DanielMartensson/STM32-Ethernet-Camera/Code/Core/Src/STM32_ILI9341_FSMC_16_Bit/ili9341.c

	/*
 * ili9341.c
 *
 *  Created on: 22 ���. 2018 �.
 *      Author: Andriy Honcharenko
 */
#include "../STM32_ILI9341_FSMC_16_Bit/ili9341.h"

#include <stdlib.h>
#include <stdarg.h>
#include <stdio.h>

/* Axis measurement */
#define CMD_X_AXIS								0x50
#define CMD_Y_AXIS								0x10
#define CMD_Z_AXIS								0x30

/* For the touch */
SPI_HandleTypeDef *_hspi;

enum {
  MemoryAccessControlNormalOrder,
  MemoryAccessControlReverseOrder
} MemoryAccessControlRefreshOrder;

enum {
	MemoryAccessControlColorOrderRGB,
	MemoryAccessControlColorOrderBGR
} MemoryAccessControlColorOrder;

static lcdPropertiesTypeDef  lcdProperties = { ILI9341_PIXEL_WIDTH, ILI9341_PIXEL_HEIGHT, LCD_ORIENTATION_PORTRAIT,true, true };
static lcdFontPropTypeDef lcdFont = {COLOR_YELLOW, COLOR_BLACK, &Font12, 1};
static lcdCursorPosTypeDef cursorXY = {0, 0};

static unsigned char lcdPortraitConfig = 0;
static unsigned char lcdLandscapeConfig = 0;
static unsigned char lcdPortraitMirrorConfig = 0;
static unsigned char lcdLandscapeMirrorConfig = 0;

static void				lcdDrawPixels(uint16_t x, uint16_t y, uint16_t *data, uint32_t dataLength);
static void        		lcdReset(void);
static void        		lcdWriteCommand(unsigned char command);
static void             lcdWriteData(unsigned short data);
static unsigned short	lcdReadData(void);

static unsigned char    lcdBuildMemoryAccessControlConfig(
                                bool rowAddressOrder,
                                bool columnAddressOrder,
                                bool rowColumnExchange,
                                bool verticalRefreshOrder,
                                bool colorOrder,
                                bool horizontalRefreshOrder);


void lcdInit(SPI_HandleTypeDef *hspi)
{
	/* Set touch SPI */
	_hspi = hspi;

  lcdPortraitConfig = lcdBuildMemoryAccessControlConfig(
                                                    MemoryAccessControlNormalOrder,		// rowAddressOrder
                                                    MemoryAccessControlReverseOrder,	// columnAddressOrder
                                                    MemoryAccessControlNormalOrder,		// rowColumnExchange
                                                    MemoryAccessControlNormalOrder,		// verticalRefreshOrder
                                                    MemoryAccessControlColorOrderBGR,	// colorOrder
                                                    MemoryAccessControlNormalOrder);	// horizontalRefreshOrder

  lcdLandscapeConfig = lcdBuildMemoryAccessControlConfig(
                                                    MemoryAccessControlNormalOrder,		// rowAddressOrder
                                                    MemoryAccessControlNormalOrder,		// columnAddressOrder
                                                    MemoryAccessControlReverseOrder,	// rowColumnExchange
                                                    MemoryAccessControlNormalOrder,		// verticalRefreshOrder
                                                    MemoryAccessControlColorOrderBGR,	// colorOrder
                                                    MemoryAccessControlNormalOrder);	// horizontalRefreshOrder

  lcdPortraitMirrorConfig = lcdBuildMemoryAccessControlConfig(
		  	  	  	  	  	  	  	  	  	  	  	MemoryAccessControlReverseOrder,	// rowAddressOrder
		                                            MemoryAccessControlNormalOrder,		// columnAddressOrder
		                                            MemoryAccessControlNormalOrder,		// rowColumnExchange
		                                            MemoryAccessControlNormalOrder,		// verticalRefreshOrder
		                                            MemoryAccessControlColorOrderBGR,	// colorOrder
		                                            MemoryAccessControlNormalOrder);	// horizontalRefreshOrder

  lcdLandscapeMirrorConfig = lcdBuildMemoryAccessControlConfig(
                                                    MemoryAccessControlReverseOrder,	// rowAddressOrder
                                                    MemoryAccessControlReverseOrder,	// columnAddressOrder
                                                    MemoryAccessControlReverseOrder,	// rowColumnExchange
                                                    MemoryAccessControlNormalOrder,		// verticalRefreshOrder
                                                    MemoryAccessControlColorOrderBGR,	// colorOrder
                                                    MemoryAccessControlNormalOrder);	// horizontalRefreshOrder

  lcdReset();

  lcdWriteCommand(ILI9341_DISPLAYOFF);

  lcdWriteCommand(0xCF);
  lcdWriteData(0x00);
  lcdWriteData(0x83);
  lcdWriteData(0x30);

  lcdWriteCommand(0xED);
  lcdWriteData(0x64);
  lcdWriteData(0x03);
  lcdWriteData(0x12);
  lcdWriteData(0x81);

  lcdWriteCommand(0xE8);
  lcdWriteData(0x85);
  lcdWriteData(0x01);
  lcdWriteData(0x79);

  lcdWriteCommand(0xCB);
  lcdWriteData(0x39);
  lcdWriteData(0x2C);
  lcdWriteData(0x00);
  lcdWriteData(0x34);
  lcdWriteData(0x02);

  lcdWriteCommand(0xF7);
  lcdWriteData(0x20);

  lcdWriteCommand(0xEA);
  lcdWriteData(0x00);
  lcdWriteData(0x00);

  lcdWriteCommand(ILI9341_POWERCONTROL1);
  lcdWriteData(0x26);

  lcdWriteCommand(ILI9341_POWERCONTROL2);
  lcdWriteData(0x11);

  lcdWriteCommand(ILI9341_VCOMCONTROL1);
  lcdWriteData(0x35);
  lcdWriteData(0x3E);

  lcdWriteCommand(ILI9341_VCOMCONTROL2);
  lcdWriteData(0xBE);

  lcdWriteCommand(ILI9341_MEMCONTROL);
  lcdWriteData(lcdPortraitConfig);

  lcdWriteCommand(ILI9341_PIXELFORMAT);
  lcdWriteData(0x55);

  lcdWriteCommand(ILI9341_FRAMECONTROLNORMAL);
  lcdWriteData(0x00);
  lcdWriteData(0x1B);

  lcdWriteCommand(0xF2);
  lcdWriteData(0x08);

  lcdWriteCommand(ILI9341_GAMMASET);
  lcdWriteData(0x01);

  lcdWriteCommand(ILI9341_POSITIVEGAMMCORR);
  lcdWriteData(0x1F);
  lcdWriteData(0x1A);
  lcdWriteData(0x18);
  lcdWriteData(0x0A);
  lcdWriteData(0x0F);
  lcdWriteData(0x06);
  lcdWriteData(0x45);
  lcdWriteData(0x87);
  lcdWriteData(0x32);
  lcdWriteData(0x0A);
  lcdWriteData(0x07);
  lcdWriteData(0x02);
  lcdWriteData(0x07);
  lcdWriteData(0x05);
  lcdWriteData(0x00);

  lcdWriteCommand(ILI9341_NEGATIVEGAMMCORR);
  lcdWriteData(0x00);
  lcdWriteData(0x25);
  lcdWriteData(0x27);
  lcdWriteData(0x05);
  lcdWriteData(0x10);
  lcdWriteData(0x09);
  lcdWriteData(0x3A);
  lcdWriteData(0x78);
  lcdWriteData(0x4D);
  lcdWriteData(0x05);
  lcdWriteData(0x18);
  lcdWriteData(0x0D);
  lcdWriteData(0x38);
  lcdWriteData(0x3A);
  lcdWriteData(0x1F);

  lcdWriteCommand(ILI9341_COLADDRSET);
  lcdWriteData(0x00);
  lcdWriteData(0x00);
  lcdWriteData(0x00);
  lcdWriteData(0xEF);

  lcdWriteCommand(ILI9341_PAGEADDRSET);
  lcdWriteData(0x00);
  lcdWriteData(0x00);
  lcdWriteData(0x01);
  lcdWriteData(0x3F);

  lcdWriteCommand(ILI9341_ENTRYMODE);
  lcdWriteData(0x07);

  lcdWriteCommand(ILI9341_DISPLAYFUNC);
  lcdWriteData(0x0A);
  lcdWriteData(0x82);
  lcdWriteData(0x27);
  lcdWriteData(0x00);

  lcdWriteCommand(ILI9341_SLEEPOUT);
  HAL_Delay(100);
  lcdWriteCommand(ILI9341_DISPLAYON);
  HAL_Delay(100);
  lcdWriteCommand(ILI9341_MEMORYWRITE);
}

void lcdTest(void)
{
	lcdSetWindow(0, 0, lcdProperties.width - 1, lcdProperties.height - 1);

	uint8_t stripSize = lcdProperties.height / 8;

	for (int y = 0; y < lcdProperties.height; y++)
	{
		for (int x = 0; x < lcdProperties.width; x++)
		{
		  if (y > lcdProperties.height - 1 - (stripSize * 1)) lcdWriteData(COLOR_WHITE);
		  else if (y > lcdProperties.height - 1 - (stripSize * 2)) lcdWriteData(COLOR_BLUE);
		  else if (y > lcdProperties.height - 1 - (stripSize * 3)) lcdWriteData(COLOR_GREEN);
		  else if (y > lcdProperties.height - 1 - (stripSize * 4)) lcdWriteData(COLOR_CYAN);
		  else if (y > lcdProperties.height - 1 - (stripSize * 5)) lcdWriteData(COLOR_RED);
		  else if (y > lcdProperties.height - 1 - (stripSize * 6)) lcdWriteData(COLOR_MAGENTA);
		  else if (y > lcdProperties.height - 1 - (stripSize * 7)) lcdWriteData(COLOR_YELLOW);
		  else lcdWriteData(COLOR_BLACK);
		}
	}
}

void lcdFillRGB(uint16_t color)
{
  lcdSetWindow(0, 0, lcdProperties.width - 1, lcdProperties.height - 1);
  int dimensions = lcdProperties.width * lcdProperties.height;
  while(dimensions--)
  {
    lcdWriteData(color);
  }
}

/**
 * \brief Draws a point at the specified coordinates
 *
 * \param x        x-Coordinate
 * \param y        y-Coordinate
 * \param color    Color
 *
 * \return void
 */
void lcdDrawPixel(uint16_t x, uint16_t y, uint16_t color)
{
    // Clip
    if ((x < 0) || (y < 0) || (x >= lcdProperties.width) || (y >= lcdProperties.height))
        return;

    lcdSetWindow(x, y, x, y);
    lcdWriteData(color);
}

void lcdDrawHLine(uint16_t x0, uint16_t x1, uint16_t y, uint16_t color)
{
  // Allows for slightly better performance than setting individual pixels

	if (x1 < x0)
	{
		// Switch x1 and x0
		swap(x0, x1);
	}

	// Check limits
	if (x1 >= lcdProperties.width)
	{
		x1 = lcdProperties.width - 1;
	}

	if (x0 >= lcdProperties.width)
	{
		x0 = lcdProperties.width - 1;
	}

	lcdSetWindow(x0, y, x1, y);

	for (int line = x0; line <= x1; line++)
	{
		lcdWriteData(color);
	}
}

void lcdDrawVLine(uint16_t x, uint16_t y0, uint16_t y1, uint16_t color)
{
  if (y1 < y0)
  {
	  swap(y0, y1);
  }

  if (x >= lcdProperties.width)
  {
    x = lcdProperties.width - 1;
  }

  if (y0 >= lcdProperties.height)
  {
    y0 = lcdProperties.height - 1;
  }

  if (y1 >= lcdProperties.height)
  {
    y1 = lcdProperties.height - 1;
  }

  lcdSetWindow(x, y0, x, y1);

  for(int line = y0; line <= y1; line++)
  {
	  lcdWriteData(color);
  }
}

/**
 * \brief Draws a line connecting the two points specified by the coordinate pairs
 *
 * \param x0	The x-coordinate of the first point
 * \param y0	The y-coordinate of the first point
 * \param x1	The x-coordinate of the second point
 * \param y1	The y-coordinate of the second point.
 * \param color	Color
 *
 * \return void
 */
void lcdDrawLine(int16_t x1, int16_t y1, int16_t x2, int16_t y2, uint16_t color)
{
	// Bresenham's algorithm - thx wikpedia

	int16_t steep = abs(y2 - y1) > abs(x2 - x1);
	if (steep)
	{
		swap(x1, y1);
		swap(x2, y2);
	}

	if (x1 > x2)
	{
		swap(x1, x2);
		swap(y1, y2);
	}

	int16_t dx, dy;
	dx = x2 - x1;
	dy = abs(y2 - y1);

	int16_t err = dx / 2;
	int16_t ystep;

	if (y1 < y2)
	{
		ystep = 1;
	}
	else
	{
		ystep = -1;
	}

	for (; x1 <= x2; x1++)
	{
		if (steep)
		{
			lcdDrawPixel(y1, x1, color);
		}
		else
		{
			lcdDrawPixel(x1, y1, color);
		}
		err -= dy;
		if (err < 0)
		{
			y1 += ystep;
			err += dx;
		}
	}
}

/**
 * \brief Draws a rectangle specified by a coordinate pair, a width, and a height.
 *
 * \param x			The x-coordinate of the upper-left corner of the rectangle to draw
 * \param y			The y-coordinate of the upper-left corner of the rectangle to draw
 * \param w			Width of the rectangle to draw
 * \param h			Height of the rectangle to draw
 * \param color		Color
 *
 * \return void
 */
void lcdDrawRect(int16_t x, int16_t y, int16_t w, int16_t h, uint16_t color)
{
	lcdDrawHLine(x, x + w - 1, y, color);
	lcdDrawHLine(x, x + w - 1, y + h - 1, color);
	lcdDrawVLine(x, y, y + h - 1, color);
	lcdDrawVLine(x + w - 1, y, y + h - 1, color);
}

/**
 * \brief Draws a rectangle with rounded corners specified by a coordinate pair, a width, and a height.
 *
 * \param x			The x-coordinate of the upper-left corner of the rectangle to draw
 * \param y			The y-coordinate of the upper-left corner of the rectangle to draw
 * \param w			Width of the rectangle to draw
 * \param h			Height of the rectangle to draw
 * \param r			Radius
 * \param color		Color
 *
 * \return void
 */
void lcdDrawRoundRect(int16_t x, int16_t y, int16_t w, int16_t h, int16_t r, uint16_t color)
{
	// smarter version
	lcdDrawHLine(x + r, x + w - r, y, color);
	lcdDrawHLine(x + r, x + w - r, y + h - 1, color);
	lcdDrawVLine(x, y + r, y + h - r, color);
	lcdDrawVLine(x + w - 1, y + r, y + h - r, color);

	// draw four corners
	lcdDrawCircleHelper(x + r, y + r, r, 1, color);
	lcdDrawCircleHelper(x + w - r - 1, y + r, r, 2, color);
	lcdDrawCircleHelper(x + w - r - 1, y + h - r - 1, r, 4, color);
	lcdDrawCircleHelper(x + r, y + h - r - 1, r, 8, color);
}

/**
 * \brief Helper function drawing rounded corners
 *
 * \param x0			The x-coordinate
 * \param y0			The y-coordinate
 * \param r				Radius
 * \param cornername	Corner (1, 2, 3, 4)
 * \param color			Color
 *
 * \return void
 */
void lcdDrawCircleHelper(int16_t x0, int16_t y0, int16_t r, uint8_t cornername, uint16_t color)
{
	int16_t f = 1 - r;
	int16_t ddF_x = 1;
	int16_t ddF_y = -2 * r;
	int16_t x = 0;
	int16_t y = r;

	while (x < y)
	{
		if (f >= 0)
		{
			y--;
			ddF_y += 2;
			f += ddF_y;
		}
		x++;
		ddF_x += 2;
		f += ddF_x;
		if (cornername & 0x4)
		{
			lcdDrawPixel(x0 + x, y0 + y, color);
			lcdDrawPixel(x0 + y, y0 + x, color);
		}
		if (cornername & 0x2)
		{
			lcdDrawPixel(x0 + x, y0 - y, color);
			lcdDrawPixel(x0 + y, y0 - x, color);
		}
		if (cornername & 0x8)
		{
			lcdDrawPixel(x0 - y, y0 + x, color);
			lcdDrawPixel(x0 - x, y0 + y, color);
		}
		if (cornername & 0x1)
		{
			lcdDrawPixel(x0 - y, y0 - x, color);
			lcdDrawPixel(x0 - x, y0 - y, color);
		}
	}
}

/**
 * \brief Draws an circle defined by a pair of coordinates and radius
 *
 * \param x0		The x-coordinate
 * \param y0		The y-coordinate
 * \param r			Radius
 * \param color		Color
 *
 * \return void
 */
void lcdDrawCircle(int16_t x0, int16_t y0, int16_t r, uint16_t color)
{
	int16_t f = 1 - r;
	int16_t ddF_x = 1;
	int16_t ddF_y = -2 * r;
	int16_t x = 0;
	int16_t y = r;

	lcdDrawPixel(x0, y0 + r, color);
	lcdDrawPixel(x0, y0 - r, color);
	lcdDrawPixel(x0 + r, y0, color);
	lcdDrawPixel(x0 - r, y0, color);

	while (x < y)
	{
		if (f >= 0)
		{
			y--;
			ddF_y += 2;
			f += ddF_y;
		}
		x++;
		ddF_x += 2;
		f += ddF_x;

		lcdDrawPixel(x0 + x, y0 + y, color);
		lcdDrawPixel(x0 - x, y0 + y, color);
		lcdDrawPixel(x0 + x, y0 - y, color);
		lcdDrawPixel(x0 - x, y0 - y, color);
		lcdDrawPixel(x0 + y, y0 + x, color);
		lcdDrawPixel(x0 - y, y0 + x, color);
		lcdDrawPixel(x0 + y, y0 - x, color);
		lcdDrawPixel(x0 - y, y0 - x, color);
	}
}

/**************************************************************************/
/*!
   @brief   Draw a triangle with no fill color
    @param    x0  Vertex #0 x coordinate
    @param    y0  Vertex #0 y coordinate
    @param    x1  Vertex #1 x coordinate
    @param    y1  Vertex #1 y coordinate
    @param    x2  Vertex #2 x coordinate
    @param    y2  Vertex #2 y coordinate
    @param    color 16-bit 5-6-5 Color to draw with
*/
/**************************************************************************/
void lcdDrawTriangle(int16_t x0, int16_t y0, int16_t x1, int16_t y1, int16_t x2, int16_t y2, uint16_t color)
{
    lcdDrawLine(x0, y0, x1, y1, color);
    lcdDrawLine(x1, y1, x2, y2, color);
    lcdDrawLine(x2, y2, x0, y0, color);
}

/**
 * \brief Draws a filled circle defined by a pair of coordinates and radius
 *
 * \param x0		The x-coordinate
 * \param y0		The y-coordinate
 * \param r			Radius
 * \param color		Color
 *
 * \return void
 */
void lcdFillCircle(int16_t x0, int16_t y0, int16_t r, uint16_t color)
{
	lcdDrawVLine(x0, y0 - r, y0 + r + 1, color);
	lcdFillCircleHelper(x0, y0, r, 3, 0, color);
}

/**
 * \brief Helper function to draw a filled circle
 *
 * \param x0			The x-coordinate
 * \param y0			The y-coordinate
 * \param r				Radius
 * \param cornername	Corner (1, 2, 3, 4)
 * \param delta			Delta
 * \param color			Color
 *
 * \return void
 */
void lcdFillCircleHelper(int16_t x0, int16_t y0, int16_t r, uint8_t cornername, int16_t delta, uint16_t color)
{
	int16_t f = 1 - r;
	int16_t ddF_x = 1;
	int16_t ddF_y = -2 * r;
	int16_t x = 0;
	int16_t y = r;

	while (x < y)
	{
		if (f >= 0)
		{
			y--;
			ddF_y += 2;
			f += ddF_y;
		}
		x++;
		ddF_x += 2;
		f += ddF_x;

		if (cornername & 0x1)
		{
			lcdDrawVLine(x0 + x, y0 - y, y0 + y + 1 + delta, color);
			lcdDrawVLine(x0 + y, y0 - x, y0 + x + 1 + delta, color);
		}
		if (cornername & 0x2)
		{
			lcdDrawVLine(x0 - x, y0 - y, y0 + y + 1 + delta, color);
			lcdDrawVLine(x0 - y, y0 - x, y0 + x + 1 + delta, color);
		}
	}
}

/**
 * \brief Draws a filled rectangle specified by a coordinate pair, a width, and a height.
 *
 * \param x				The x-coordinate of the upper-left corner of the rectangle to draw
 * \param y				The y-coordinate of the upper-left corner of the rectangle to draw
 * \param w				Width of the rectangle to draw
 * \param h				Height of the rectangle to draw
 * \param fillcolor		Color
 *
 * \return void
 */
void lcdFillRect(int16_t x, int16_t y, int16_t w, int16_t h, uint16_t fillcolor)
{
	// clipping
	if((x >= lcdProperties.width) || (y >= lcdProperties.height)) return;
	if((x + w - 1) >= lcdProperties.width) w = lcdProperties.width - x;
	if((y + h - 1) >= lcdProperties.height) h = lcdProperties.height - y;

	for(int16_t y1 = y; y1 <= y + h; y1++)
	{
		lcdDrawHLine(x, x + w, y1, fillcolor);
	}
}

/**
 * \brief Draws a filled rounded rectangle specified by a coordinate pair, a width, and a height.
 *
 * \param x				The x-coordinate of the upper-left corner of the rectangle to draw
 * \param y				The y-coordinate of the upper-left corner of the rectangle to draw
 * \param w				Width of the rectangle to draw
 * \param h				Height of the rectangle to draw
 * \param r				Radius
 * \param fillcolor		Color
 *
 * \return void
 */
void lcdFillRoundRect(int16_t x, int16_t y, int16_t w, int16_t h, int16_t r, uint16_t color)
{
	// smarter version
	lcdFillRect(x + r, y, w - 2 * r, h, color);

	// draw four corners
	lcdFillCircleHelper(x + w - r - 1, y + r, r, 1, h - 2 * r - 1, color);
	lcdFillCircleHelper(x + r, y + r, r, 2, h - 2 * r - 1, color);
}


/**************************************************************************/
/*!
   @brief     Draw a triangle with color-fill
    @param    x0  Vertex #0 x coordinate
    @param    y0  Vertex #0 y coordinate
    @param    x1  Vertex #1 x coordinate
    @param    y1  Vertex #1 y coordinate
    @param    x2  Vertex #2 x coordinate
    @param    y2  Vertex #2 y coordinate
    @param    color 16-bit 5-6-5 Color to fill/draw with
*/
/**************************************************************************/
void lcdFillTriangle(int16_t x0, int16_t y0, int16_t x1, int16_t y1, int16_t x2, int16_t y2, uint16_t color)
{

    int16_t a, b, y, last;

    // Sort coordinates by Y order (y2 >= y1 >= y0)
    if (y0 > y1)
    {
        swap(y0, y1); swap(x0, x1);
    }
    if (y1 > y2)
    {
        swap(y2, y1); swap(x2, x1);
    }
    if (y0 > y1)
    {
        swap(y0, y1); swap(x0, x1);
    }

    if(y0 == y2)
    { // Handle awkward all-on-same-line case as its own thing
        a = b = x0;
        if(x1 < a)      a = x1;
        else if(x1 > b) b = x1;
        if(x2 < a)      a = x2;
        else if(x2 > b) b = x2;
        lcdDrawHLine(a, b + 1, y0, color);
        return;
    }

    int16_t
    dx01 = x1 - x0,
    dy01 = y1 - y0,
    dx02 = x2 - x0,
    dy02 = y2 - y0,
    dx12 = x2 - x1,
    dy12 = y2 - y1;
    int32_t
    sa   = 0,
    sb   = 0;

    // For upper part of triangle, find scanline crossings for segments
    // 0-1 and 0-2.  If y1=y2 (flat-bottomed triangle), the scanline y1
    // is included here (and second loop will be skipped, avoiding a /0
    // error there), otherwise scanline y1 is skipped here and handled
    // in the second loop...which also avoids a /0 error here if y0=y1
    // (flat-topped triangle).
    if(y1 == y2) last = y1;   // Include y1 scanline
    else         last = y1-1; // Skip it

    for(y=y0; y<=last; y++)
    {
        a   = x0 + sa / dy01;
        b   = x0 + sb / dy02;
        sa += dx01;
        sb += dx02;
        /* longhand:
        a = x0 + (x1 - x0) * (y - y0) / (y1 - y0);
        b = x0 + (x2 - x0) * (y - y0) / (y2 - y0);
        */
        if(a > b) swap(a,b);
        lcdDrawHLine(a, b + 1, y, color);
    }

    // For lower part of triangle, find scanline crossings for segments
    // 0-2 and 1-2.  This loop is skipped if y1=y2.
    sa = (int32_t)dx12 * (y - y1);
    sb = (int32_t)dx02 * (y - y0);
    for(; y<=y2; y++)
    {
        a   = x1 + sa / dy12;
        b   = x0 + sb / dy02;
        sa += dx12;
        sb += dx02;
        /* longhand:
        a = x1 + (x2 - x1) * (y - y1) / (y2 - y1);
        b = x0 + (x2 - x0) * (y - y0) / (y2 - y0);
        */
        if(a > b) swap(a,b);
        lcdDrawHLine(a, b + 1, y, color);
    }
}

void lcdDrawImage(uint16_t x, uint16_t y, GUI_CONST_STORAGE GUI_BITMAP* pBitmap)
{
	if((x >= lcdProperties.width) || (y >= lcdProperties.height)) return;
	if((x + pBitmap->xSize - 1) >= lcdProperties.width) return;
	if((y + pBitmap->ySize - 1) >= lcdProperties.height) return;
	uint32_t dataLength = pBitmap->bytesPerLine / (pBitmap->bitsPerPixel / 8);

	for (int i = 0; i < pBitmap->ySize; i++)
		lcdDrawPixels(x, y + i, (uint16_t*)(pBitmap->pData + i * pBitmap->bytesPerLine), dataLength);
}

void lcdHome(void)
{
	cursorXY.x = 0;
	cursorXY.y = 0;
	lcdSetWindow(0, 0, lcdProperties.width - 1, lcdProperties.height - 1);
}


/**
 * \brief Draws a character at the specified coordinates
 *
 * \param x			The x-coordinate
 * \param y			The y-coordinate
 * \param c			Character
 * \param color		Character color
 * \param bg		Background color
 * \param size		Character Size
 *
 * \return void
 */
void lcdDrawChar(int16_t x, int16_t y, unsigned char c, uint16_t color, uint16_t bg)
{
	if ((x >= lcdProperties.width) || 			// Clip right
			(y >= lcdProperties.height) || 		// Clip bottom
			((x + lcdFont.pFont->Width) < 0) || // Clip left
			((y + lcdFont.pFont->Height) < 0))  // Clip top
		return;

	uint8_t fontCoeff = lcdFont.pFont->Height / 8;
	uint8_t xP = 0;

	for(uint8_t i = 0; i < lcdFont.pFont->Height; i++)
	{
		uint8_t line;

		for(uint8_t k = 0; k < fontCoeff; k++)
		{
			line = lcdFont.pFont->table[((c - 0x20) * lcdFont.pFont->Height * fontCoeff) + (i * fontCoeff) + k];

			for(uint8_t j = 0; j < 8; j++)
			{
				if((line & 0x80) == 0x80)
				{
					lcdDrawPixel(x + j + xP, y + i, color);
				}
				else if (bg != color)
				{
					lcdDrawPixel(x + j + xP, y + i, bg);
				}
				line <<= 1;
			}

			xP += 8;
		}

		xP = 0;
	}
}

/**
 * \brief Print the specified Text
 *
 * \param fmt	Format text
 * \param
 *
 * \return void
 */
void lcdPrintf(const char *fmt, ...)
{
	static char buf[256];
	char *p;
	va_list lst;

	va_start(lst, fmt);
	vsprintf(buf, fmt, lst);
	va_end(lst);

	p = buf;
	while (*p)
	{
		if (*p == '\n')
		{
			cursorXY.y += lcdFont.pFont->Height;
			cursorXY.x = 0;
		}
		else if (*p == '\r')
		{
			// skip em
		}
		else if (*p == '\t')
		{
			cursorXY.x += lcdFont.pFont->Width * 4;
		}
		else
		{
			lcdDrawChar(cursorXY.x, cursorXY.y, *p, lcdFont.TextColor, lcdFont.BackColor);
			cursorXY.x += lcdFont.pFont->Width;
			if (lcdFont.TextWrap && (cursorXY.x > (lcdProperties.width - lcdFont.pFont->Width)))
			{
				cursorXY.y += lcdFont.pFont->Height;
				cursorXY.x = 0;
			}
		}
		p++;

		if (cursorXY.y >= lcdProperties.height)
		{
			cursorXY.y = 0;
		}
	}
}



/**
 * \brief Sets the font
 *
 * \param font pointer font
 *
 * \return void
 */
void lcdSetTextFont(sFONT* font)
{
	lcdFont.pFont = font;
}

/**
 * \brief Sets the text color
 *
 * \param c		Text color
 * \param b		Background color
 *
 * \return void
 */
void lcdSetTextColor(uint16_t c, uint16_t b)
{
	lcdFont.TextColor = c;
	lcdFont.BackColor = b;
}

/**
 * \brief Set Text wrap
 *
 * \param w
 *
 * \return void
 */
void lcdSetTextWrap(uint8_t w)
{
	lcdFont.TextWrap = w;
}

void lcdSetOrientation(lcdOrientationTypeDef value)
{
	lcdProperties.orientation = value;
	lcdWriteCommand(ILI9341_MEMCONTROL);

	switch (lcdProperties.orientation)
	{
		case LCD_ORIENTATION_PORTRAIT:
			lcdWriteData(lcdPortraitConfig);
			lcdProperties.width = ILI9341_PIXEL_WIDTH;
			lcdProperties.height = ILI9341_PIXEL_HEIGHT;
			break;
		case LCD_ORIENTATION_PORTRAIT_MIRROR:
			lcdWriteData(lcdPortraitMirrorConfig);
			lcdProperties.width = ILI9341_PIXEL_WIDTH;
			lcdProperties.height = ILI9341_PIXEL_HEIGHT;
			break;
		case LCD_ORIENTATION_LANDSCAPE:
			lcdWriteData(lcdLandscapeConfig);
			lcdProperties.width = ILI9341_PIXEL_HEIGHT;
			lcdProperties.height = ILI9341_PIXEL_WIDTH;
			break;
		case LCD_ORIENTATION_LANDSCAPE_MIRROR:
			lcdWriteData(lcdLandscapeMirrorConfig);
			lcdProperties.width = ILI9341_PIXEL_HEIGHT;
			lcdProperties.height = ILI9341_PIXEL_WIDTH;
			break;
		default:
			break;
	}

	//lcdWriteCommand(ILI9341_MEMORYWRITE);
	lcdSetWindow(0, 0, lcdProperties.width - 1, lcdProperties.height - 1);
}

void lcdSetCursor(unsigned short x, unsigned short y)
{
	cursorXY.x = x;
	cursorXY.y = y;
	lcdSetWindow(x, y, x, y);
}

/**
 * \brief Sets window address
 *
 * \param x0         Left top window x-coordinate
 * \param y0         Left top window y-coordinate
 * \param x1         Rigth bottom window x-coordinate
 * \param y1         Rigth bottom window y-coordinate
 *
 * \return void
 */
void lcdSetWindow(unsigned short x0, unsigned short y0, unsigned short x1, unsigned short y1)
{
  lcdWriteCommand(ILI9341_COLADDRSET);
  lcdWriteData((x0 >> 8) & 0xFF);
  lcdWriteData(x0 & 0xFF);
  lcdWriteData((x1 >> 8) & 0xFF);
  lcdWriteData(x1 & 0xFF);
  lcdWriteCommand(ILI9341_PAGEADDRSET);
  lcdWriteData((y0 >> 8) & 0xFF);
  lcdWriteData(y0 & 0xFF);
  lcdWriteData((y1 >> 8) & 0xFF);
  lcdWriteData(y1 & 0xFF);
  lcdWriteCommand(ILI9341_MEMORYWRITE);
}

void lcdBacklightOff(void)
{
	LCD_BL_OFF();
}

void lcdBacklightOn(void)
{
	LCD_BL_ON();
}

void lcdInversionOff(void)
{
	lcdWriteCommand(ILI9341_INVERTOFF);
}

void lcdInversionOn(void)
{
	lcdWriteCommand(ILI9341_INVERTON);
}

void lcdDisplayOff(void)
{
	lcdWriteCommand(ILI9341_DISPLAYOFF);
	LCD_BL_OFF();
}

void lcdDisplayOn(void)
{
	lcdWriteCommand(ILI9341_DISPLAYON);
	LCD_BL_ON();
}

void lcdTearingOff(void)
{
	lcdWriteCommand(ILI9341_TEARINGEFFECTOFF);
}

void lcdTearingOn(bool m)
{
	lcdWriteCommand(ILI9341_TEARINGEFFECTON);
	lcdWriteData(m);
}

uint16_t lcdGetWidth(void)
{
  return lcdProperties.width;
}

uint16_t lcdGetHeight(void)
{
  return lcdProperties.height;
}

uint16_t lcdGetControllerID(void)
{
	uint16_t id;
	lcdWriteCommand(ILI9341_READID4);
	id = lcdReadData();
	id = lcdReadData();
	id = ((uint16_t) lcdReadData() << 8);
	id |= lcdReadData();
	return id;
}

lcdOrientationTypeDef lcdGetOrientation(void)
{
  return lcdProperties.orientation;
}

sFONT* lcdGetTextFont(void)
{
	return lcdFont.pFont;
}

lcdPropertiesTypeDef lcdGetProperties(void)
{
  return lcdProperties;
}

/**
 * \brief Reads a point from the specified coordinates
 *
 * \param x        x-Coordinate
 * \param y        y-Coordinate
 *
 * \return uint16_t     Color
 */
uint16_t lcdReadPixel(uint16_t x, uint16_t y)
{
    uint16_t temp[3];
    // Clip
    if ((x < 0) || (y < 0) || (x >= lcdProperties.width) || (y >= lcdProperties.height))
        return 0;

    lcdWriteCommand(ILI9341_COLADDRSET);
    lcdWriteData((x >> 8) & 0xFF);
    lcdWriteData(x & 0xFF);

    lcdWriteCommand(ILI9341_PAGEADDRSET);
    lcdWriteData((y >> 8) & 0xFF);
    lcdWriteData(y & 0xFF);

    lcdWriteCommand(ILI9341_MEMORYREAD);

    temp[0] = lcdReadData(); // dummy read
    temp[1] = lcdReadData();
    temp[2] = lcdReadData();

    return lcdColor565((temp[1] >> 8) & 0xFF, temp[1] & 0xFF, (temp[2] >> 8) & 0xFF);
}

uint16_t lcdColor565(uint8_t r, uint8_t g, uint8_t b)
{
	return ((r & 0xF8) << 8) | ((g & 0xFC) << 3) | (b >> 3);
}

/*---------Static functions--------------------------*/

static void lcdDrawPixels(uint16_t x, uint16_t y, uint16_t *data, uint32_t dataLength)
{
  uint32_t i = 0;

  lcdSetWindow(x, y, lcdProperties.width - 1, lcdProperties.height - 1);

  do
  {
    lcdWriteData(data[i++]);
  }
  while (i < dataLength);
}

static void lcdReset(void)
{
	lcdWriteCommand(ILI9341_SOFTRESET);
	HAL_Delay(50);
}

// Write an 8 bit command to the IC driver
static void lcdWriteCommand(unsigned char command)
{
	LCD_CmdWrite(command);
}

// Write an 16 bit data word to the IC driver
static void lcdWriteData(unsigned short data)
{
	LCD_DataWrite(data);
}

static unsigned short lcdReadData(void)
{
	return LCD_DataRead();
}

static unsigned char lcdBuildMemoryAccessControlConfig(
                        bool rowAddressOrder,
                        bool columnAddressOrder,
                        bool rowColumnExchange,
                        bool verticalRefreshOrder,
                        bool colorOrder,
                        bool horizontalRefreshOrder)
{
  unsigned char value 				= 0;
  if(horizontalRefreshOrder) value 	|= ILI9341_MADCTL_MH;
  if(colorOrder) value 				|= ILI9341_MADCTL_BGR;
  if(verticalRefreshOrder) value 	|= ILI9341_MADCTL_ML;
  if(rowColumnExchange) value 		|= ILI9341_MADCTL_MV;
  if(columnAddressOrder) value 		|= ILI9341_MADCTL_MX;
  if(rowAddressOrder) value 		|= ILI9341_MADCTL_MY;
  return value;
}

// Send TSC2046 Command and wait for a response
static uint16_t TSC2046_SendCommand(uint8_t cmd) {
	uint8_t lcdBuf[3] = { 0, 0, 0 };
	uint16_t return16 = 0;
	HAL_GPIO_WritePin(TOUCH_CS_GPIO_Port, TOUCH_CS_Pin, GPIO_PIN_RESET);
	lcdBuf[0] = cmd;
	HAL_SPI_Transmit(_hspi, lcdBuf, 1, 10);
	if (HAL_SPI_Receive(_hspi, &lcdBuf[1], 2, 10) == HAL_OK)
		return16 = (lcdBuf[1] << 4) + (lcdBuf[2] >> 4);
	else
		return16 = 0;
	HAL_GPIO_WritePin(TOUCH_CS_GPIO_Port, TOUCH_CS_Pin, GPIO_PIN_SET);
	return return16;
}

// Get x-axis raw touch 12-bit value
static uint16_t TSC2046_getRaw_X() {
	return TSC2046_SendCommand(CMD_X_AXIS | 0x84); // 0x84 = Command default
}
// Get y-axis raw touch 12-bit value
static uint16_t TSC2046_getRaw_Y() {
	return TSC2046_SendCommand(CMD_Y_AXIS | 0x84); // 0x84 = Command default
}
/*Get z-axis raw touch 12-bit value - Not used any longer due to TS_IRQ
static uint16_t TSC2046_getRaw_Z() {
	return TSC2046_SendCommand(CMD_Z_AXIS | 0x84); // 0x84 = Command default
}*/

// Print calibration point - Top-Left corner point
static void TSC2046_TL_point() {
	lcdFillCircle(10, 10, 3, COLOR_RED);
	lcdSetCursor(20, 30);
	lcdSetTextColor(COLOR_RED, COLOR_BLACK);
	lcdPrintf("Press here");
}
// Print calibration point - Bottom-Right corner point
static void TSC2046_BR_point() {
	lcdFillCircle(lcdProperties.width - 10, lcdProperties.height - 10, 3, COLOR_RED);
	lcdSetCursor(lcdProperties.width - 80, lcdProperties.height - 40);
	lcdSetTextColor(COLOR_RED, COLOR_BLACK);
	lcdPrintf("Press here");
}

// Poll for touch status
static void TSC2046_GetRawTouch() {

	// Assign raw touch based on orientation
	switch (lcdProperties.orientation) {
	case LCD_ORIENTATION_LANDSCAPE_MIRROR:
		lcdProperties.localRawTouch.x_touch = 4095 - TSC2046_getRaw_X();
		lcdProperties.localRawTouch.y_touch = TSC2046_getRaw_Y();
		lcdProperties.myTS_Calibrate.Width = 240;
		lcdProperties.myTS_Calibrate.Height = 320;
		break;

	case LCD_ORIENTATION_LANDSCAPE:
		lcdProperties.localRawTouch.x_touch = 4095 - TSC2046_getRaw_Y();
		lcdProperties.localRawTouch.y_touch = 4095 - TSC2046_getRaw_X();
		lcdProperties.myTS_Calibrate.Width = 320;
		lcdProperties.myTS_Calibrate.Height = 240;
		break;

	case LCD_ORIENTATION_PORTRAIT:
		lcdProperties.localRawTouch.x_touch = TSC2046_getRaw_X();
		lcdProperties.localRawTouch.y_touch = 4095 - TSC2046_getRaw_Y();
		lcdProperties.myTS_Calibrate.Width = 240;
		lcdProperties.myTS_Calibrate.Height = 320;
		break;

	case LCD_ORIENTATION_PORTRAIT_MIRROR:
		lcdProperties.localRawTouch.x_touch = TSC2046_getRaw_Y();
		lcdProperties.localRawTouch.y_touch = TSC2046_getRaw_X();
		lcdProperties.myTS_Calibrate.Width = 320;
		lcdProperties.myTS_Calibrate.Height = 240;
		break;
	}
	// These are for the calibration
	lcdProperties.myRawTouchDef.x_touch = lcdProperties.localRawTouch.x_touch;
	lcdProperties.myRawTouchDef.y_touch = lcdProperties.localRawTouch.y_touch;
}

// Get touch screen data when calibration is already made
static void TSC2046_GetData() {
	// Reset
	uint16_t temp16x = 0, temp16y = 0;
	// Read touch data
	for (uint8_t i = 0; i < 10; i++) {
		TSC2046_GetRawTouch();
		temp16x += lcdProperties.localRawTouch.x_touch;
		temp16y += lcdProperties.localRawTouch.y_touch;
	}
	lcdProperties.localRawTouch.x_touch = temp16x * 0.1;
	lcdProperties.localRawTouch.y_touch = temp16y * 0.1;

	// X-axis value
	lcdProperties.myTsData.X = lcdProperties.myTS_Calibrate.Scale_X * lcdProperties.localRawTouch.x_touch + lcdProperties.myTS_Calibrate.Bias_X;

	// Y-axis value
	lcdProperties.myTsData.Y = lcdProperties.myTS_Calibrate.Scale_Y * lcdProperties.localRawTouch.y_touch + lcdProperties.myTS_Calibrate.Bias_Y;
}

// Calibrate resistive touch panel
void touchCalibrate() {
	// Set rotation
	lcdSetOrientation(lcdProperties.orientation);

	// Reset
	lcdProperties.myTS_Calibrate.TL_X = 0;
	lcdProperties.myTS_Calibrate.TL_Y = 0;
	lcdProperties.myTS_Calibrate.BR_X = 0;
	lcdProperties.myTS_Calibrate.BR_Y = 0;
	lcdProperties.myRawTouchDef.y_touch = 0;
	lcdProperties.myRawTouchDef.x_touch = 0;

	// Get Top-Left corner calibration coordinate
	TSC2046_TL_point();
	while (1) {
		if (touchIsPressed()) {
			for (uint8_t i = 0; i < 10; i++) {
				TSC2046_GetRawTouch();
				lcdProperties.myTS_Calibrate.TL_X += lcdProperties.myRawTouchDef.x_touch;
				lcdProperties.myTS_Calibrate.TL_Y += lcdProperties.myRawTouchDef.y_touch;
			}
			break;
		}
		HAL_Delay(10);
	}
	HAL_Delay(1000);

	// Get Bottom-Right corner calibration coordinate
	TSC2046_BR_point();
	while (1) {
		if (touchIsPressed()) {
			for (uint8_t i = 0; i < 10; i++) {
				TSC2046_GetRawTouch();
				lcdProperties.myTS_Calibrate.BR_X += lcdProperties.myRawTouchDef.x_touch;
				lcdProperties.myTS_Calibrate.BR_Y += lcdProperties.myRawTouchDef.y_touch;
			}
			break;
		}
		HAL_Delay(10);
	}

	lcdProperties.myTS_Calibrate.TL_X *= 0.1;
	lcdProperties.myTS_Calibrate.TL_Y *= 0.1;

	lcdProperties.myTS_Calibrate.BR_X *= 0.1;
	lcdProperties.myTS_Calibrate.BR_Y *= 0.1;

	// Calculate scalar
	lcdProperties.myTS_Calibrate.Scale_X = (lcdProperties.myTS_Calibrate.Width + 0.0f) / (lcdProperties.myTS_Calibrate.BR_X - lcdProperties.myTS_Calibrate.TL_X + 0.0f);
	lcdProperties.myTS_Calibrate.Scale_Y = (lcdProperties.myTS_Calibrate.Height + 0.0f) / (lcdProperties.myTS_Calibrate.BR_Y - lcdProperties.myTS_Calibrate.TL_Y + 0.0f);

	// Calculate bias
	lcdProperties.myTS_Calibrate.Bias_X = -1 - lcdProperties.myTS_Calibrate.Scale_X * lcdProperties.myTS_Calibrate.TL_X; // -1 is for bias. Change this so you have 100% accuracy at center of the LCD
	lcdProperties.myTS_Calibrate.Bias_Y = -1 - lcdProperties.myTS_Calibrate.Scale_Y * lcdProperties.myTS_Calibrate.TL_Y; // -1 is for bias. Change this so you have 100% accuracy at center of the LCD
}

void touchGetCalibrationParameters(float *Scale_X, float *Scale_Y, float *Bias_X, float *Bias_Y) {
	*Scale_X = lcdProperties.myTS_Calibrate.Scale_X;
	*Scale_Y = lcdProperties.myTS_Calibrate.Scale_Y;
	*Bias_X = lcdProperties.myTS_Calibrate.Bias_X;
	*Bias_Y = lcdProperties.myTS_Calibrate.Bias_Y;
}

void touchSetCalibrationParameters(float *Scale_X, float *Scale_Y, float *Bias_X, float *Bias_Y) {
	lcdProperties.myTS_Calibrate.Scale_X = *Scale_X;
	lcdProperties.myTS_Calibrate.Scale_Y = *Scale_Y;
	lcdProperties.myTS_Calibrate.Bias_X = *Bias_X;
	lcdProperties.myTS_Calibrate.Bias_Y = *Bias_Y;
}

bool touchIsPressed() {
	static uint8_t count = 0;
	static bool has_been_pressed = false;
	bool pressed = (bool) !HAL_GPIO_ReadPin(TOUCH_IRQ_GPIO_Port, TOUCH_IRQ_Pin); // TS_IRQ goes low when LCD being pressed on
	if(pressed == true && has_been_pressed == false){
		has_been_pressed = true;
		count = 0;
		HAL_Delay(100); /* Wait until the finger have fully pressed the LCD screen. The Touch SPI and Touch Interrupt are different things */
		return true;
	} else {
		/* This is only for debouncing */
		if(pressed == false && has_been_pressed == true) {
			count = 1 + count;
			if(count >= 10)
				has_been_pressed = false;
		}else{
			count = 0;
		}
		return false;
	}
}

void touchPrintCoordinates(){
	TSC2046_GetData();
	char text[30];
	sprintf(text, "X:%i,Y:%i", lcdProperties.myTsData.X, lcdProperties.myTsData.Y);
	lcdFillRGB(COLOR_BLACK);
	lcdSetTextColor(COLOR_RED, COLOR_BLACK);
	lcdSetCursor(lcdProperties.myTsData.X, lcdProperties.myTsData.Y);
	lcdPrintf(text);
}
