DanielMartensson/STM32-Ethernet-Camera/Code/Core/Src/OV7670/ov7670.h

/*
 * ov7670.h
 *
 *  Created on: May 7, 2022
 *      Author: Daniel Mårtensson
 */

#ifndef SRC_OV7670_OV7670_H_
#define SRC_OV7670_OV7670_H_

#include "main.h"
#include <stdint.h>

#endif /* SRC_OV7670_OV7670_H_ */
